Queens-Rocket-Engineering-Team/av-power/Firmware/Hybrid_Power_Module/src/node.cpp

#include "node.h"

#include <aim_job.h>
#include <aim_flight_recorder.h>

static uint32_t s_batteryMv = 12000U;
static uint32_t s_5vMv = 0U;
static uint32_t s_gseMv = 0U;
static int32_t s_i3v3Ma = 0;
static int32_t s_i24vMa = 0;

// --- ADC & Voltage Divider Calibration (constexpr) ---
constexpr uint32_t kAdcVrefMv     = 3300U;  // 3.3V reference
constexpr uint32_t kAdcMaxCounts  = 4095U;  // 12-bit ADC resolution

constexpr uint32_t calcDividerMaxMv(uint32_t r1, uint32_t r2) {
  return (kAdcVrefMv * (r1 + r2)) / r2;
}

// Battery Sense: R1=30k, R2=10k -> Max 13,200 mV (13.2V)
constexpr uint32_t kBattR1    = 30000U;
constexpr uint32_t kBattR2    = 10000U;
constexpr uint32_t kBattMaxMv = calcDividerMaxMv(kBattR1, kBattR2);

// 5V Sense: R1=10k, R2=10k -> Max 6,600 mV (6.6V)
constexpr uint32_t k5vR1      = 10000U;
constexpr uint32_t k5vR2      = 10000U;
constexpr uint32_t k5vMaxMv   = calcDividerMaxMv(k5vR1, k5vR2);

// GSE 24V Sense: R1=100k, R2=10k -> Max 36,300 mV (36.3V)
constexpr uint32_t kGseR1     = 100000U;
constexpr uint32_t kGseR2     = 10000U;
constexpr uint32_t kGseMaxMv  = calcDividerMaxMv(kGseR1, kGseR2);

inline uint32_t adcToMv(uint32_t rawAdc, uint32_t fullScaleMv) {
  return (rawAdc * fullScaleMv) / kAdcMaxCounts;
}

static aim::Job s_telemetryJob{1000U};
static aim::Job s_logJob(1000U);  // 1 Hz flight log

static void updateLed(aim::NodeState state) {
  static aim::NodeState s_lastState = static_cast<aim::NodeState>(0xFF);
  if (state == s_lastState) return;
  s_lastState = state;
  digitalWrite(pins::kDebugLed, (state == aim::NodeState::Nominal) ? HIGH : LOW);
}

void nodeInit() {
  pinMode(pins::kDebugLed, OUTPUT);
  digitalWrite(pins::kDebugLed, LOW);

  // Enable 3.3V ACS current sensor power (PA4)
  pinMode(pins::k3V3AcsPower, OUTPUT);
  digitalWrite(pins::k3V3AcsPower, HIGH);

  // Keep 5V ACS current sensor power disabled (PA6)
  // !!! DO NOT POWER ON (using wrong current sense could break mcu)
  pinMode(pins::k5VAcsPower, OUTPUT);
  digitalWrite(pins::k5VAcsPower, LOW);

  // Set STM32 ADC resolution to 12-bit (0-4095)
  analogReadResolution(12);

  // Configure ADC pins as inputs
  pinMode(pins::kBatterySense, INPUT);
  pinMode(pins::k5VSense, INPUT);
  pinMode(pins::kGseSense, INPUT);
  pinMode(pins::k3V3CurrentSense, INPUT);
  pinMode(pins::k24VCurrentSense, INPUT);

  LOG_INFO("Power telemetry pins initialized");
}

void nodeUpdate(uint32_t nowMs) {
  updateLed(nodeCurrentState());
  (void)nowMs;

  // Sample voltages using constexpr full-scale calibration
  s_batteryMv = adcToMv(static_cast<uint32_t>(analogRead(pins::kBatterySense)), kBattMaxMv);
  s_5vMv      = adcToMv(static_cast<uint32_t>(analogRead(pins::k5VSense)),      k5vMaxMv);
  s_gseMv     = adcToMv(static_cast<uint32_t>(analogRead(pins::kGseSense)),     kGseMaxMv);

  // 3.3V current sensor (U4: ACS37041-010B3, 1.65V zero point, 132 mV/A)
  int32_t v3v3IMv = (static_cast<int32_t>(analogRead(pins::k3V3CurrentSense)) * 3300) / 4095;
  s_i3v3Ma = ((v3v3IMv - 1650) * 1000) / 132;

  // 24V current sensor (U6: INA187A1, 20 V/V gain across 100mOhm shunt -> 2 V/A -> 2 mV/mA)
  int32_t v24vIMv = (static_cast<int32_t>(analogRead(pins::k24VCurrentSense)) * 3300) / 4095;
  s_i24vMa = v24vIMv / 2;
}

void nodeServiceLog(uint32_t nowMs, AimFlightRecorder& recorder) {
  if (!s_logJob.due(nowMs)) return;

  uint32_t rowData[kLogCols] = {nowMs, s_batteryMv, s_5vMv, s_gseMv};
  recorder.writeRow(rowData, nowMs);
}

void nodeServiceCanTx(uint32_t nowMs, AimNetwork& aim) {
  if (s_telemetryJob.due(nowMs)) {
    aim::Msg voltMsg = {};
    voltMsg.cls = aim::Class::Sensor;
    voltMsg.subject = aim::subject::BattVolt;
    voltMsg.setSensorValue(static_cast<int32_t>(s_batteryMv));
    (void)aim.send(voltMsg);
  }
}

void nodeOnRx(const aim::Msg& m, uint32_t nowMs) {
  (void)m;
  (void)nowMs;
}

aim::NodeState nodeCurrentState() {
  return aim::NodeState::Nominal;
}

uint16_t nodeErrorBits() {
  return 0U;
}

// Accessor definitions
uint32_t nodeGetBatteryMv() { return s_batteryMv; }
uint32_t nodeGet5vMv() { return s_5vMv; }
uint32_t nodeGetGseMv() { return s_gseMv; }
int32_t nodeGet3v3CurrentMa() { return s_i3v3Ma; }
int32_t nodeGet24vCurrentMa() { return s_i24vMa; }

#ifndef FLIGHT_BUILD
static void hookPowerSnapshot(Stream& out) {
  out.print("V_BATT=");
  out.print(s_batteryMv);
  out.println(" mV");

  out.print("5V_PSU=");
  out.print(s_5vMv);
  out.println(" mV");

  out.print("24V_GSE=");
  out.print(s_gseMv);
  out.println(" mV");

  out.print("I_3V3=");
  out.print(s_i3v3Ma);
  out.println(" mA");

  out.print("I_24V=");
  out.print(s_i24vMa);
  out.println(" mA");

  out.println("I_5V=disabled (HW issue - unpowered)");
}

static const AimConsoleHook s_consoleHooks[] = {
  {'p', "power snapshot", hookPowerSnapshot},
};

const AimConsoleHook* nodeConsoleHooks(uint8_t& count) {
  count = sizeof(s_consoleHooks) / sizeof(s_consoleHooks[0]);
  return s_consoleHooks;
}
#endif
